GreenBotics/greenbotics-yatoopi/docs/blog/2016-02-02/2016-02-02_00.jpg

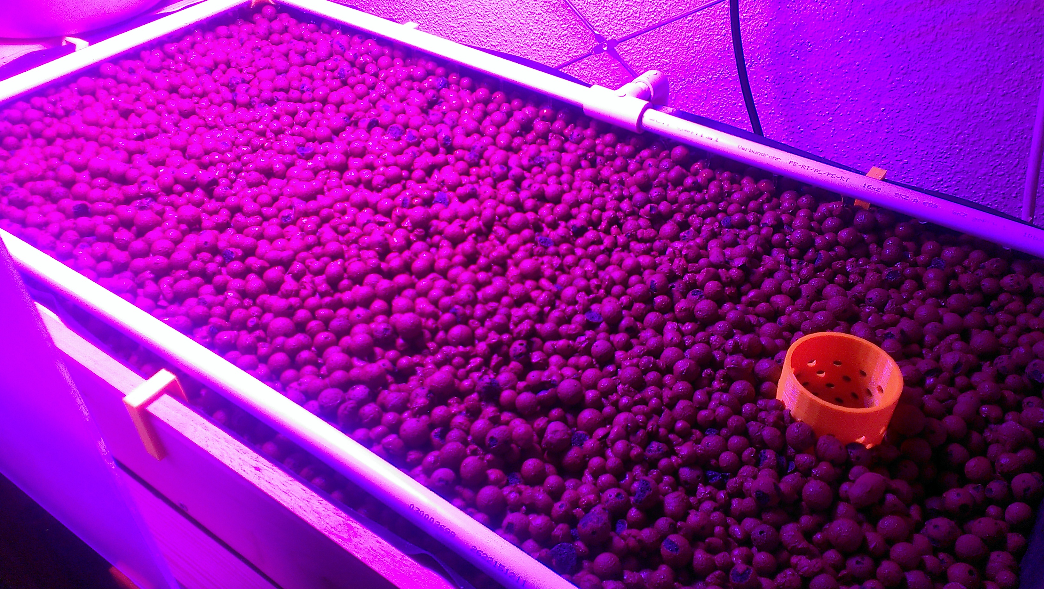
docs/blog/2016-02-02/2016-02-02_00.jpg
