GreenBotics/greenbotics-yatoopi/cad/growbed/bed-corners/aquaponics-bed-corner.stl

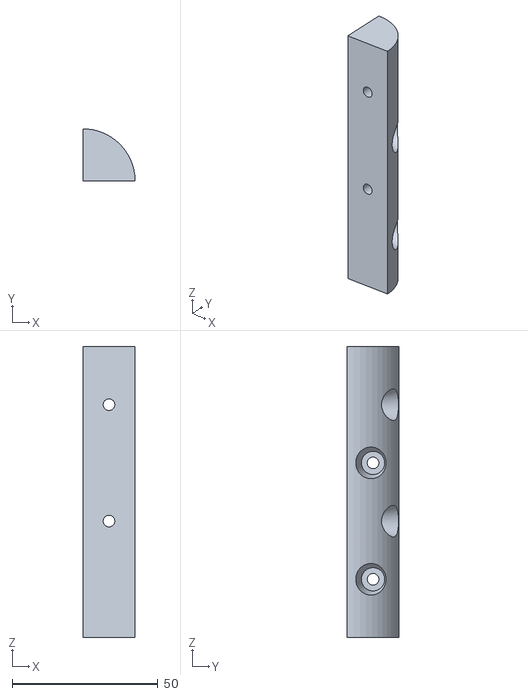
[picture p19: CAD file, 2015-02-08]
cad/growbed/bed-corners/aquaponics-bed-corner.stl
18.0 x 18.0 x 100.0
