GreenBotics/greenbotics-yatoopi/cad/piping/aquarium-mounts/sideTubingHolder-m22-0.0.1.stl

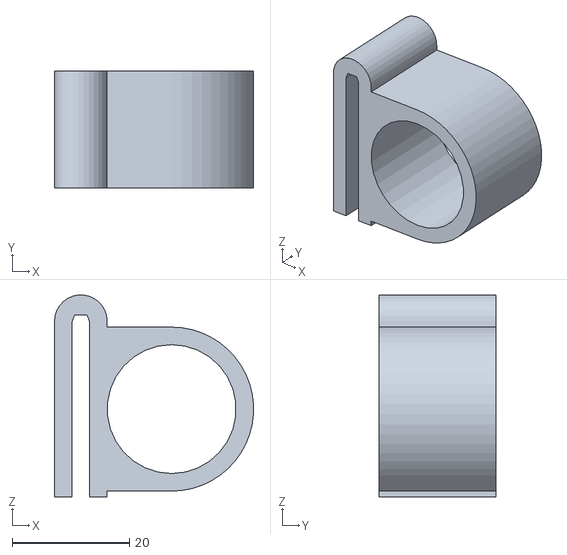
[picture p20: CAD file, 2015-12-12]
cad/piping/aquarium-mounts/sideTubingHolder-m22-0.0.1.stl
34.0 x 20.0 x 34.5
