GreenBotics/greenbotics-yatoopi/cad/piping/syphon-system/custom_syphon_bucket_out_6mm.stl

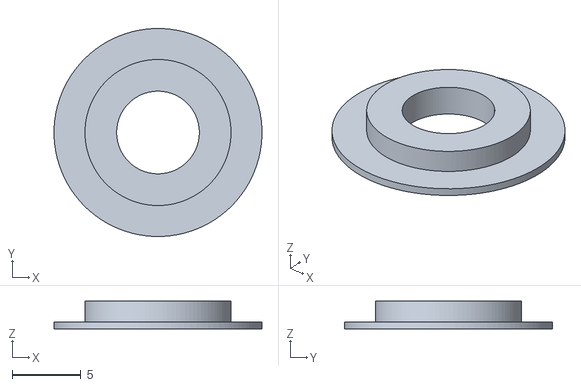
[picture p21: CAD file, 2015-12-31]
cad/piping/syphon-system/custom_syphon_bucket_out_6mm.stl
15.1 x 15.1 x 2.00
