GreenBotics/greenbotics-yatoopi/cad/accessories/webcam-holder/webcam-holder-top-0.0.2.stl

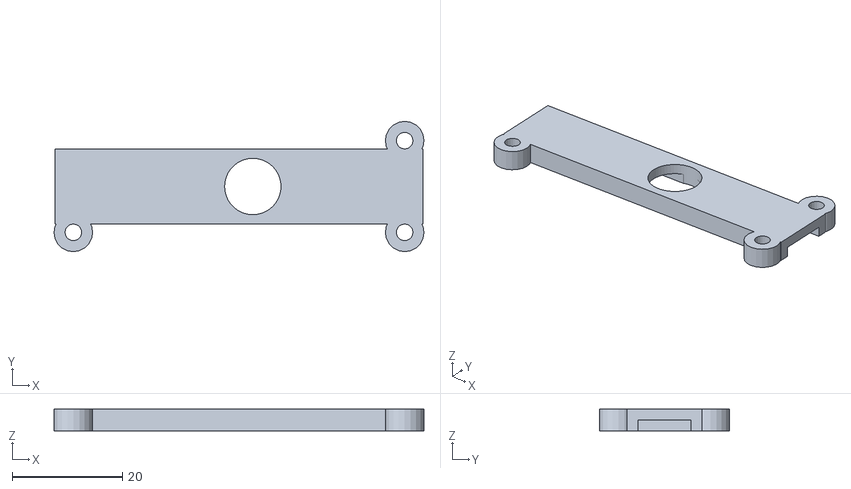
[picture p22: CAD file, 2015-02-08]
cad/accessories/webcam-holder/webcam-holder-top-0.0.2.stl
67.0 x 23.6 x 3.98
