GreenBotics/greenbotics-yatoopi/cad/piping/aquarium-mounts/cornerTubingHolder-0.0.1.stl

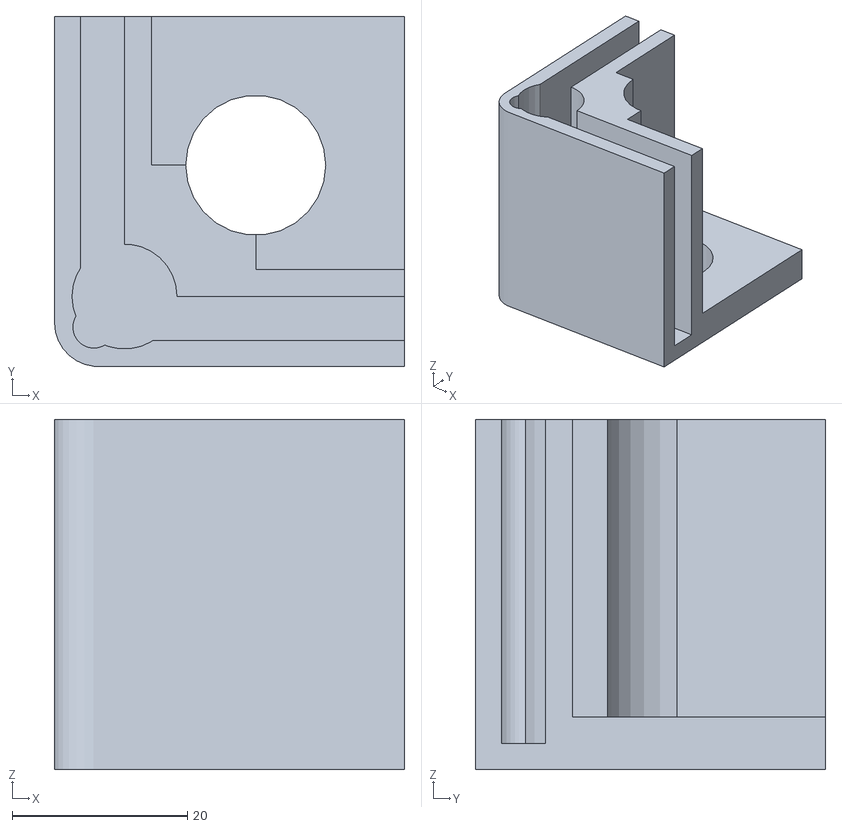
[picture p23: CAD file, 2015-05-24]
cad/piping/aquarium-mounts/cornerTubingHolder-0.0.1.stl
40.0 x 40.0 x 40.0
