GreenBotics/greenbotics-yatoopi/cad/piping/syphon-system/custom_syphon_hinge_lever.stl

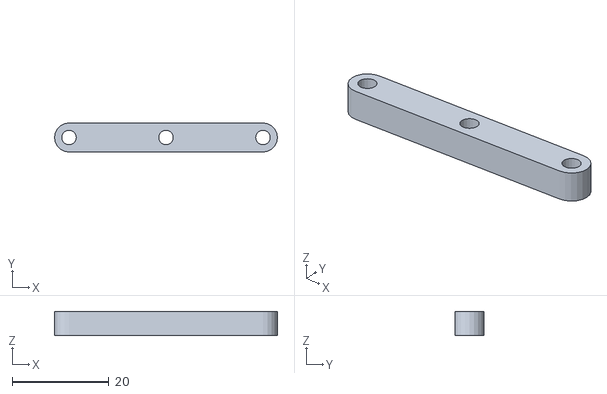
[picture p24: CAD file, 2015-12-30]
cad/piping/syphon-system/custom_syphon_hinge_lever.stl
46.0 x 6.00 x 5.00
