GreenBotics/greenbotics-yatoopi/cad/accessories/webcam-holder/webcam-holder-top-0.0.1-test.stl

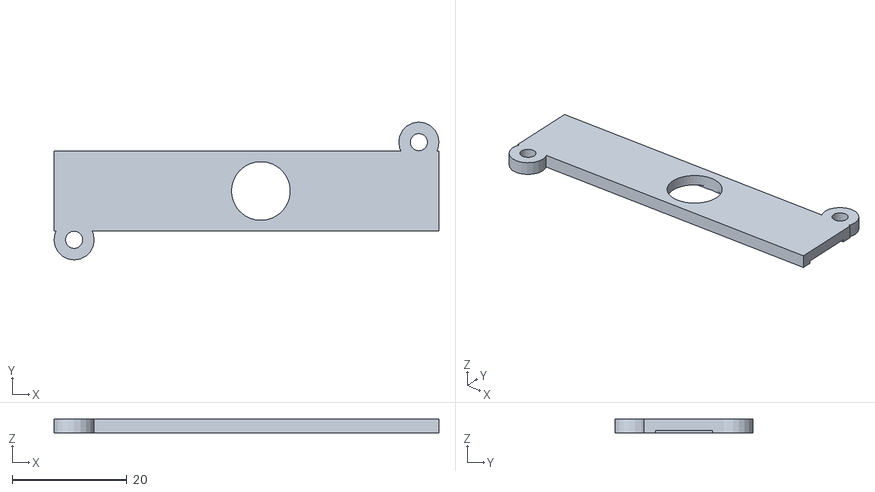
[picture p25: CAD file, 2015-02-08]
cad/accessories/webcam-holder/webcam-holder-top-0.0.1-test.stl
67.0 x 24.0 x 2.50
