GreenBotics/greenbotics-yatoopi/cad/piping/syphon-system/custom_syphon_hinge_center.stl

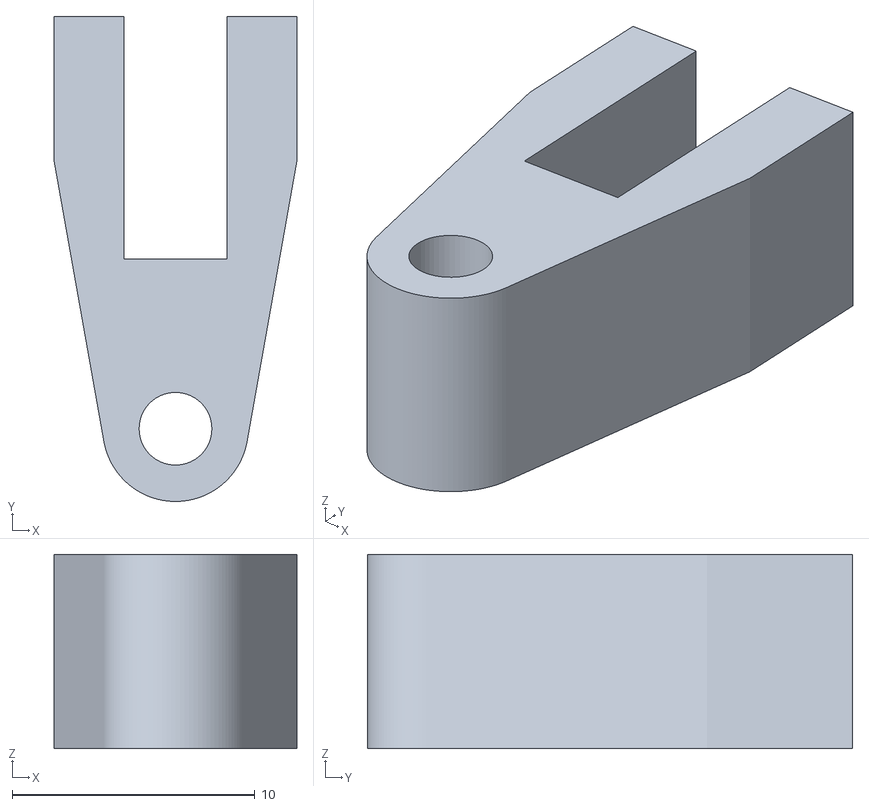
[picture p26: CAD file, 2015-12-30]
cad/piping/syphon-system/custom_syphon_hinge_center.stl
10.0 x 20.0 x 8.00
