GreenBotics/greenbotics-yatoopi/cad/piping/syphon-system/custom_syphon_valve.stl

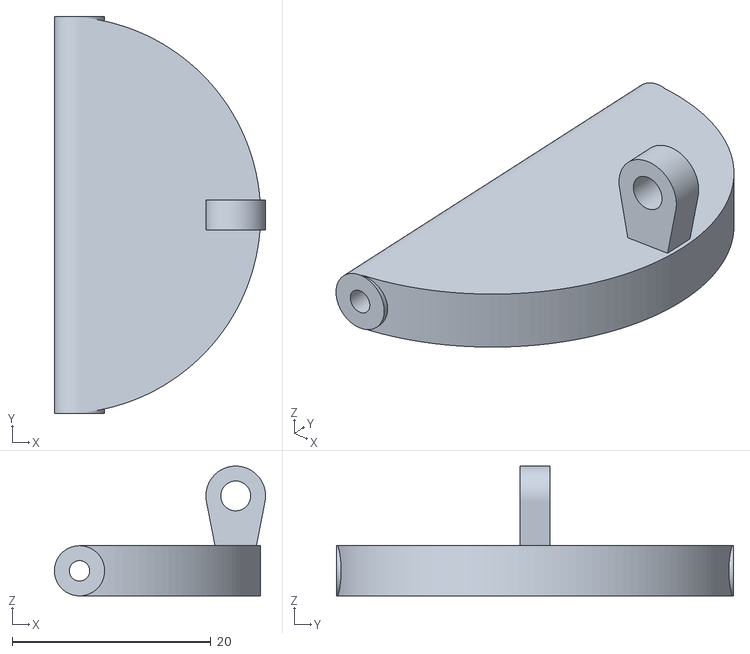
[picture p27: CAD file, 2015-12-30]
cad/piping/syphon-system/custom_syphon_valve.stl
21.2 x 39.9 x 13.1
