GreenBotics/greenbotics-yatoopi/cad/piping/syphon-system/custom_syphon_bucket.stl

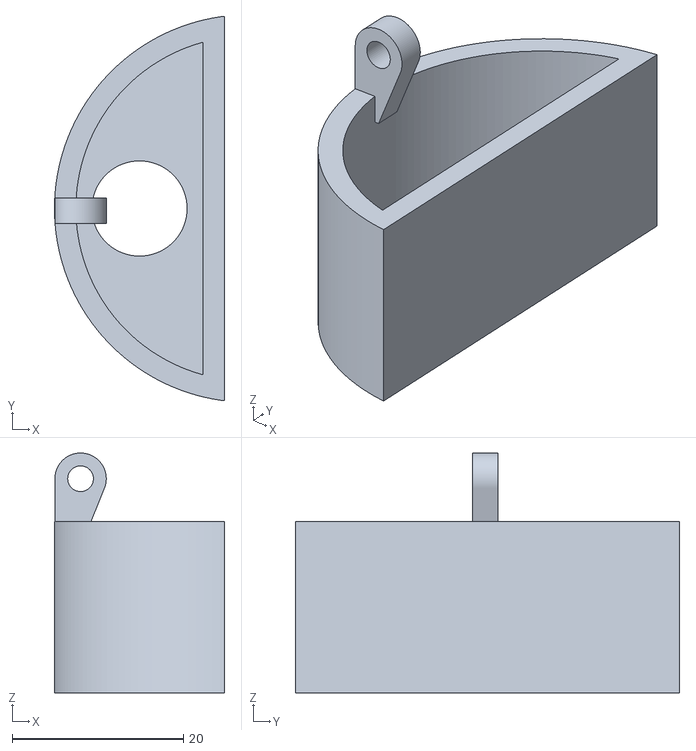
[picture p28: CAD file, 2015-12-30]
cad/piping/syphon-system/custom_syphon_bucket.stl
19.9 x 44.9 x 28.0
