GreenBotics/greenbotics-yatoopi/cad/piping/syphon-system/custom_syphon_spout_wall.stl

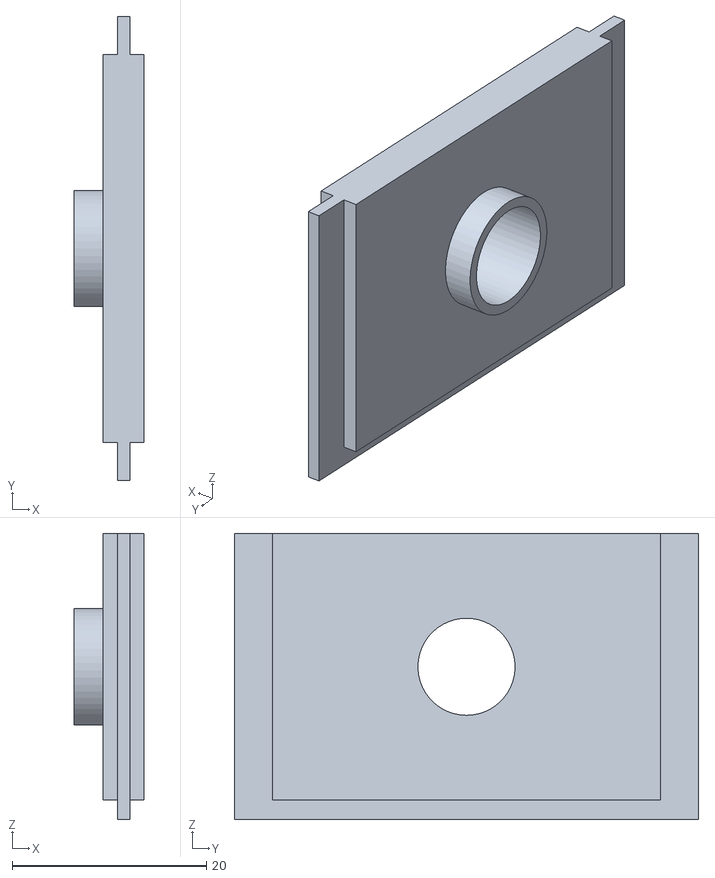
[picture p29: CAD file, 2015-12-30]
cad/piping/syphon-system/custom_syphon_spout_wall.stl
7.25 x 47.8 x 29.5
