GreenBotics/greenbotics-yatoopi/cad/piping/syphon-system/custom_syphon_container.stl

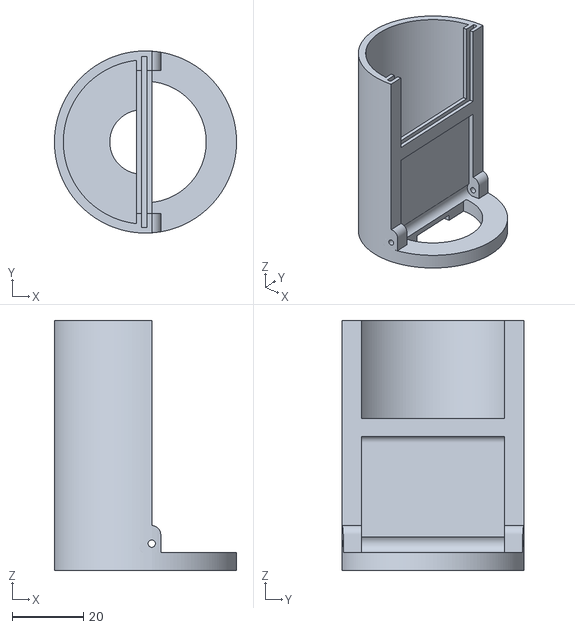
[picture p30: CAD file, 2015-12-29]
cad/piping/syphon-system/custom_syphon_container.stl
51.0 x 51.0 x 70.0
