GreenBotics/greenbotics-yatoopi/cad/piping/syphon-system/bell_syphon_0.0.1.stl

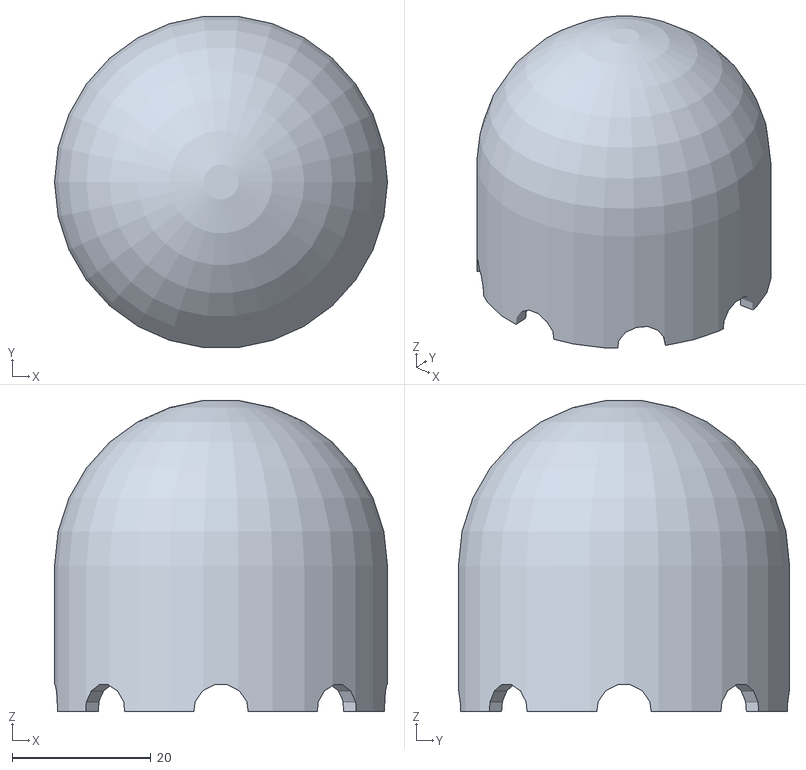
[picture p31: CAD file, 2015-12-12]
cad/piping/syphon-system/bell_syphon_0.0.1.stl
48.0 x 47.7 x 44.9
